Qrome/marquee-scroller/images/3b64f9842db7e2d93067fb12060f99eb_preview_featured.jpg

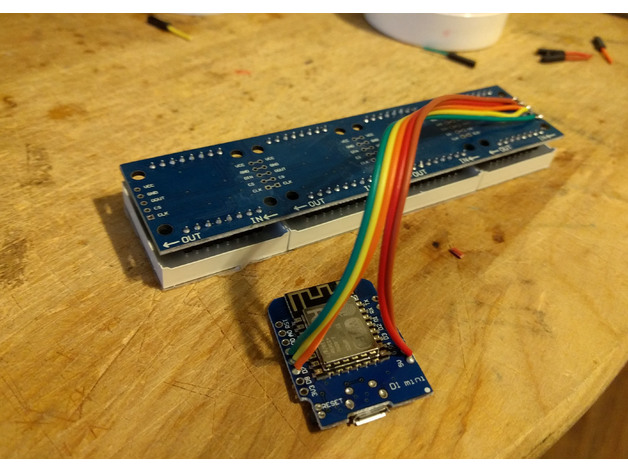
images/3b64f9842db7e2d93067fb12060f99eb_preview_featured.jpg
