Qrome/marquee-scroller/images/3efd24abfa85b82bd10c75c7d18ff65a_preview_featured.jpg

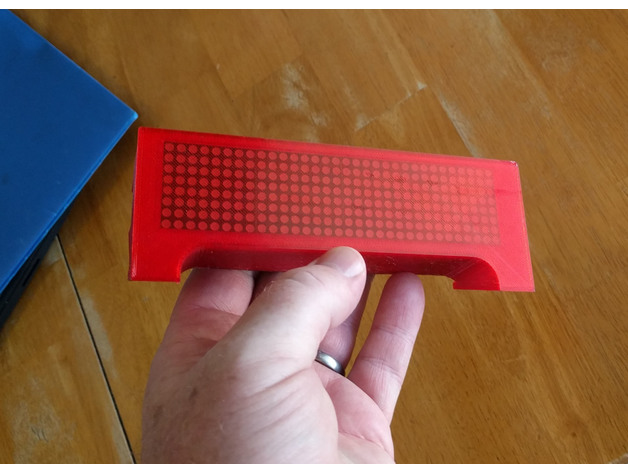
images/3efd24abfa85b82bd10c75c7d18ff65a_preview_featured.jpg
