Qrome/marquee-scroller/images/4b506a5f4453a4dca707494d488074df_preview_featured.jpg

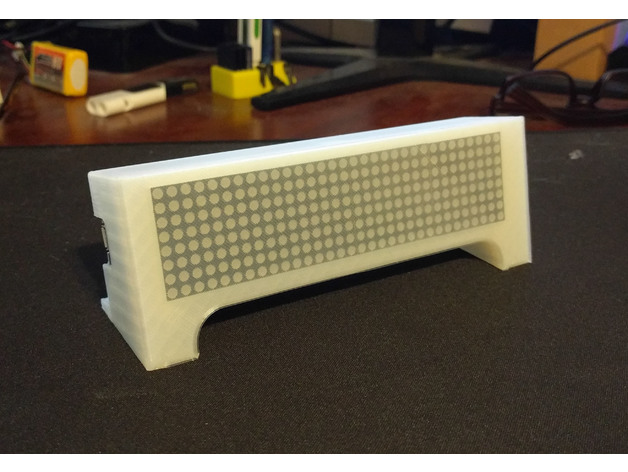
images/4b506a5f4453a4dca707494d488074df_preview_featured.jpg
