Qrome/marquee-scroller/images/7204e0794c823191f16de0fdef62f2f2_preview_featured.jpg

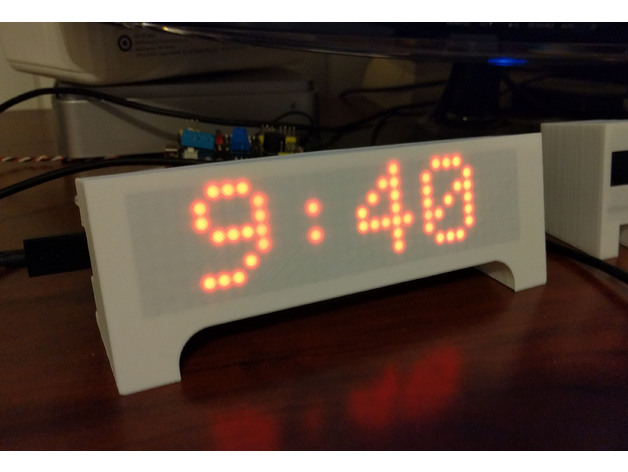
images/7204e0794c823191f16de0fdef62f2f2_preview_featured.jpg
