Qrome/marquee-scroller/images/db4c485a8160105baa86e0b669c0f4a7_preview_featured.jpg

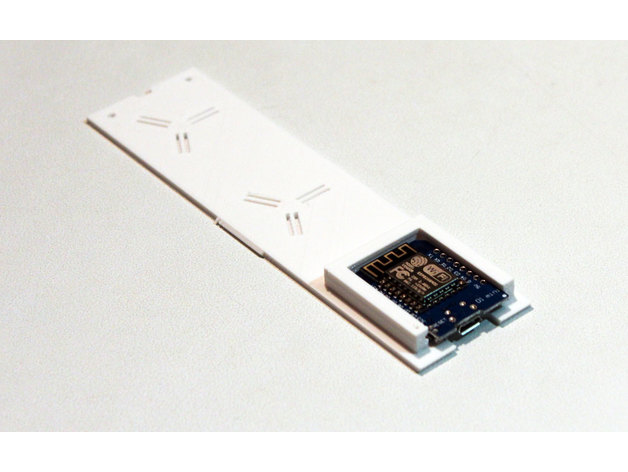
images/db4c485a8160105baa86e0b669c0f4a7_preview_featured.jpg
