Qrome/marquee-scroller/images/f312fa6ae253fd21f8e5bca22b7c22d8_preview_featured.jpg

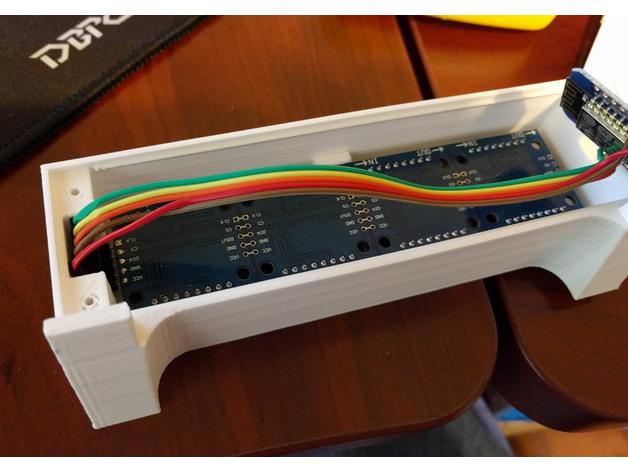
images/f312fa6ae253fd21f8e5bca22b7c22d8_preview_featured.jpg
