Qrome/marquee-scroller/marquee/OctoPrintClient.cpp

/** The MIT License (MIT)

Copyright (c) 2018 David Payne

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
THE SOFTWARE IS PROVIDED "AS IS", WITHOUT WARRANTY OF ANY KIND, EXPRESS OR
IMPLIED, INCLUDING BUT NOT LIMITED TO THE WARRANTIES OF MERCHANTABILITY,
FITNESS FOR A PARTICULAR PURPOSE AND NONINFRINGEMENT. IN NO EVENT SHALL THE
AUTHORS OR COPYRIGHT HOLDERS BE LIABLE FOR ANY CLAIM, DAMAGES OR OTHER
LIABILITY, WHETHER IN AN ACTION OF CONTRACT, TORT OR OTHERWISE, ARISING FROM,
OUT OF OR IN CONNECTION WITH THE SOFTWARE OR THE USE OR OTHER DEALINGS IN THE
SOFTWARE.
*/

#include "OctoPrintClient.h"

OctoPrintClient::OctoPrintClient(String ApiKey, String server, int port, String user, String pass) {
  updateOctoPrintClient(ApiKey, server, port, user, pass);
}

void OctoPrintClient::updateOctoPrintClient(String ApiKey, String server, int port, String user, String pass) {
  server.toCharArray(myServer, 100);
  myApiKey = ApiKey;
  myPort = port;
  encodedAuth = "";
  if (user != "") {
    String userpass = user + ":" + pass;
    base64 b64;
    encodedAuth = b64.encode(userpass, true);
  }
}

boolean OctoPrintClient::validate() {
  boolean rtnValue = false;
  printerData.error = "";
  if (String(myServer) == "") {
    printerData.error += "Server address is required; ";
  }
  if (myApiKey == "") {
    printerData.error += "ApiKey is required; ";
  }
  if (printerData.error == "") {
    rtnValue = true;
  }
  return rtnValue;
}

void OctoPrintClient::getPrinterJobResults() {
  if (!validate()) {
    return;
  }
  WiFiClient printClient;
  printClient.setTimeout(10000);
  String apiGetData = "GET /api/job HTTP/1.1";

  Serial.println("Getting Octoprint Data");
  Serial.println(apiGetData);
  result = "";
  if (printClient.connect(myServer, myPort)) {  //starts client connection, checks for connection
    printClient.println(apiGetData);
    printClient.println("Host: " + String(myServer) + ":" + String(myPort));
    printClient.println("X-Api-Key: " + myApiKey);
    if (encodedAuth != "") {
      printClient.print("Authorization: ");
      printClient.println("Basic " + encodedAuth);
    }
    printClient.println("User-Agent: ArduinoWiFi/1.1");
    printClient.println("Connection: close");
    if (printClient.println() == 0) {
      Serial.println("OctoPrint Connection failed.");
      resetPrintData();
      printerData.error = "Octoprint Connection Failed";
      return;
    }
  } 
  else {
    Serial.println("Connection for OctoPrint data failed: " + String(myServer) + ":" + String(myPort)); //error message if no client connect
    Serial.println();
    resetPrintData();
      printerData.error = "Connection for OctoPrint data failed: " + String(myServer) + ":" + String(myPort);
    return;
  }

  // Check HTTP status
  char status[32] = {0};
  printClient.readBytesUntil('\r', status, sizeof(status));
  if (strcmp(status, "HTTP/1.1 200 OK") != 0) {
    Serial.print(F("Unexpected response: "));
    Serial.println(status);
    resetPrintData();
    printerData.error = String(status);
    return;
  }

  // Skip HTTP headers
  char endOfHeaders[] = "\r\n\r\n";
  if (!printClient.find(endOfHeaders)) {
    Serial.println(F("Invalid response"));
    resetPrintData();
    printerData.error = "Invalid response";
    return;
  }

  const size_t bufferSize = JSON_OBJECT_SIZE(1) + JSON_OBJECT_SIZE(2) + JSON_OBJECT_SIZE(3) + 2*JSON_OBJECT_SIZE(5) + JSON_OBJECT_SIZE(6) + 710;
  DynamicJsonBuffer jsonBuffer(bufferSize);

  // Parse JSON object
  JsonObject& root = jsonBuffer.parseObject(printClient);
  if (!root.success()) {
    Serial.println(F("OctoPrint Data Parsing failed!"));
    return;
  }
  
  printerData.averagePrintTime = (const char*)root["job"]["averagePrintTime"];
  printerData.estimatedPrintTime = (const char*)root["job"]["estimatedPrintTime"];
  printerData.fileName = (const char*)root["job"]["file"]["name"];
  printerData.fileSize = (const char*)root["job"]["file"]["size"];
  printerData.lastPrintTime = (const char*)root["job"]["lastPrintTime"];
  printerData.progressCompletion = (const char*)root["progress"]["completion"];
  printerData.progressFilepos = (const char*)root["progress"]["filepos"];
  printerData.progressPrintTime = (const char*)root["progress"]["printTime"];
  printerData.progressPrintTimeLeft = (const char*)root["progress"]["printTimeLeft"];
  printerData.state = (const char*)root["state"];

  if (isPrinting()) {
    Serial.println("Status: " + printerData.state + " " + printerData.fileName + "(" + printerData.progressCompletion + "%)");
  } else if (isOperational()) {
    Serial.println("Status: " + printerData.state);
  } else {
    Serial.println("Printer Not Opperational");
  }
  
  printClient.stop(); //stop client
}

// Reset all PrinterData
void OctoPrintClient::resetPrintData() {
  printerData.averagePrintTime = "";
  printerData.estimatedPrintTime = "";
  printerData.fileName = "";
  printerData.fileSize = "";
  printerData.lastPrintTime = "";
  printerData.progressCompletion = "";
  printerData.progressFilepos = "";
  printerData.progressPrintTime = "";
  printerData.progressPrintTimeLeft = "";
  printerData.state = "";
  printerData.error = "";
}

String OctoPrintClient::getAveragePrintTime(){
  return printerData.averagePrintTime;
}

String OctoPrintClient::getEstimatedPrintTime() {
  return printerData.estimatedPrintTime;
}

String OctoPrintClient::getFileName() {
  return printerData.fileName;
}

String OctoPrintClient::getFileSize() {
  return printerData.fileSize;
}

String OctoPrintClient::getLastPrintTime(){
  return printerData.lastPrintTime;
}

String OctoPrintClient::getProgressCompletion() {
  return String(printerData.progressCompletion.toInt());
}

String OctoPrintClient::getProgressFilepos() {
  return printerData.progressFilepos;  
}

String OctoPrintClient::getProgressPrintTime() {
  return printerData.progressPrintTime;
}

String OctoPrintClient::getProgressPrintTimeLeft() {
  return printerData.progressPrintTimeLeft;
}

String OctoPrintClient::getState() {
  return printerData.state;
}

boolean OctoPrintClient::isPrinting() {
  boolean printing = false;
  if (printerData.state == "Printing") {
    printing = true;
  }
  return printing;
}

boolean OctoPrintClient::isOperational() {
  boolean operational = false;
  if (printerData.state == "Operational") {
    operational = true;
  }
  return operational;
}

String OctoPrintClient::getError() {
  return printerData.error;
}
