Qrome/marquee-scroller/marquee/TimeDB.cpp

/** The MIT License (MIT)

Copyright (c) 2019 magnum129@github

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
THE SOFTWARE IS PROVIDED "AS IS", WITHOUT WARRANTY OF ANY KIND, EXPRESS OR
IMPLIED, INCLUDING BUT NOT LIMITED TO THE WARRANTIES OF MERCHANTABILITY,
FITNESS FOR A PARTICULAR PURPOSE AND NONINFRINGEMENT. IN NO EVENT SHALL THE
AUTHORS OR COPYRIGHT HOLDERS BE LIABLE FOR ANY CLAIM, DAMAGES OR OTHER
LIABILITY, WHETHER IN AN ACTION OF CONTRACT, TORT OR OTHERWISE, ARISING FROM,
OUT OF OR IN CONNECTION WITH THE SOFTWARE OR THE USE OR OTHER DEALINGS IN THE
SOFTWARE.
*/

#include "TimeDB.h"

TimeDB::TimeDB(String apiKey)
{
  myApiKey = apiKey;
}

void TimeDB::updateConfig(String apiKey, String lat, String lon)
{
  myApiKey = apiKey;
  myLat = lat;
  myLon = lon;
}

time_t TimeDB::getTime()
{
  WiFiClient client;
  String apiGetData = "GET /v2.1/get-time-zone?key=" + myApiKey + "&format=json&by=position&lat=" + myLat + "&lng=" + myLon + " HTTP/1.1";
  Serial.println("Getting Time Data for " + myLat + "," + myLon);
  Serial.println(apiGetData);
  String result = "";
  if (client.connect(servername, 80)) {  //starts client connection, checks for connection
    client.println(apiGetData);
    client.println("Host: " + String(servername));
    client.println("User-Agent: ArduinoWiFi/1.1");
    client.println("Connection: close");
    client.println();
  }
  else {
    Serial.println("connection for time data failed"); //error message if no client connect
    Serial.println();
    return 20;
  }

  while (client.connected() && !client.available()) delay(1); //waits for data

  Serial.println("Waiting for data");

  boolean record = false;
  while (client.connected() || client.available()) { //connected or data available
    char c = client.read(); //gets byte from ethernet buffer
    if (String(c) == "{") {
      record = true;
    }
    if (record) {
      result = result + c;
    }
    if (String(c) == "}") {
      record = false;
    }
  }
  client.stop(); //stop client
  Serial.println(result);

  int timeStart = result.lastIndexOf('{'); // trim response to start of JSON -- issue 194
  result = result.substring(timeStart);
  char jsonArray [result.length() + 1];
  result.toCharArray(jsonArray, sizeof(jsonArray));
  jsonArray[result.length() + 1] = '\0';
  DynamicJsonBuffer json_buf;
  JsonObject& root = json_buf.parseObject(jsonArray);
  localMillisAtUpdate = millis();
  Serial.println();
  if (root["timestamp"] == 0) {
    return 20;
  } else {
    return (unsigned long) root["timestamp"];
  }
}

String TimeDB::getDayName() {
  switch (weekday()) {
    case 1:
      return "Sunday";
      break;
    case 2:
      return "Monday";
      break;
    case 3:
      return "Tuesday";
      break;
    case 4:
      return "Wednesday";
      break;
    case 5:
      return "Thursday";
      break;
    case 6:
      return "Friday";
      break;
    case 7:
      return "Saturday";
      break;
    default:
      return "";
  }
}

String TimeDB::getMonthName() {
  String rtnValue = "";
  switch (month()) {
    case 1:
      rtnValue = "Jan";
      break;
    case 2:
      rtnValue = "Feb";
      break;
    case 3:
      rtnValue = "Mar";
      break;
    case 4:
      rtnValue = "Apr";
      break;
    case 5:
      rtnValue = "May";
      break;
    case 6:
      rtnValue = "June";
      break;
    case 7:
      rtnValue = "July";
      break;
    case 8:
      rtnValue = "Aug";
      break;
    case 9:
      rtnValue = "Sep";
      break;
    case 10:
      rtnValue = "Oct";
      break;
    case 11:
      rtnValue = "Nov";
      break;
    case 12:
      rtnValue = "Dec";
      break;
    default:
      rtnValue = "";
  }
  return rtnValue;
}


String TimeDB::getAmPm() {
  String ampmValue = "AM";
  if (isPM()) {
    ampmValue = "PM";
  }
  return ampmValue;
}

String TimeDB::zeroPad(int number) {
  if (number < 10) {
    return "0" + String(number);
  } else {
    return String(number);
  }
}
